mlab-modules/SDRX01/doc/src/img/signal2.jpg

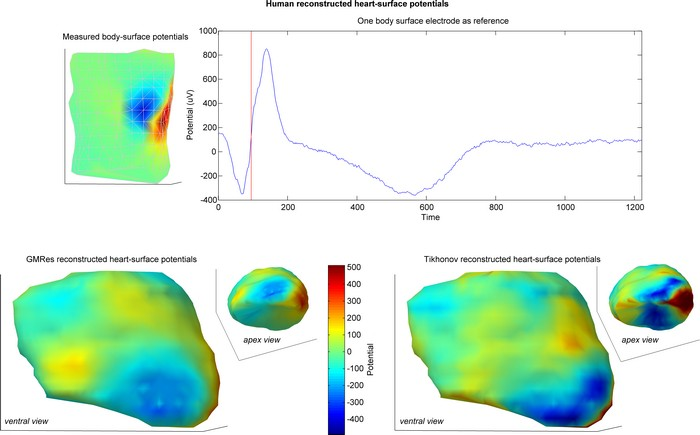
doc/src/img/signal2.jpg
