mlab-modules/SDRX01/hw/cam_doc/SDRX.pdf

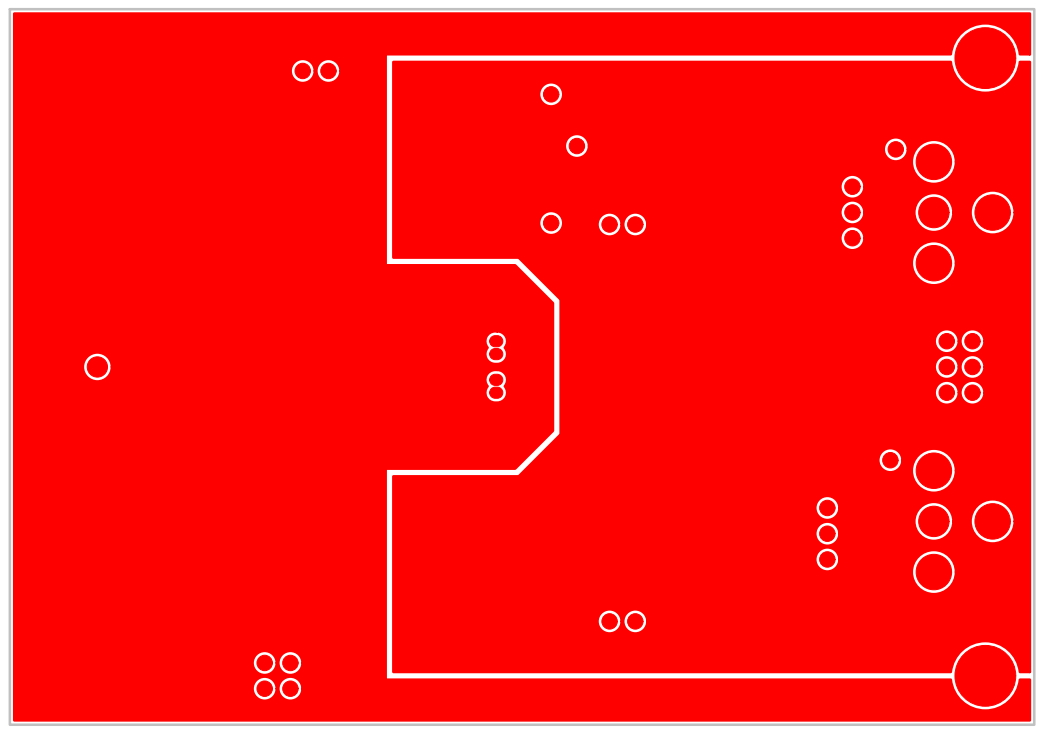
[picture p22: page 1]
M1M¹x1; M2M²x1; M4M⁴x1; M5M⁵x1; P1P¹x1 P¹x2; P¹x3

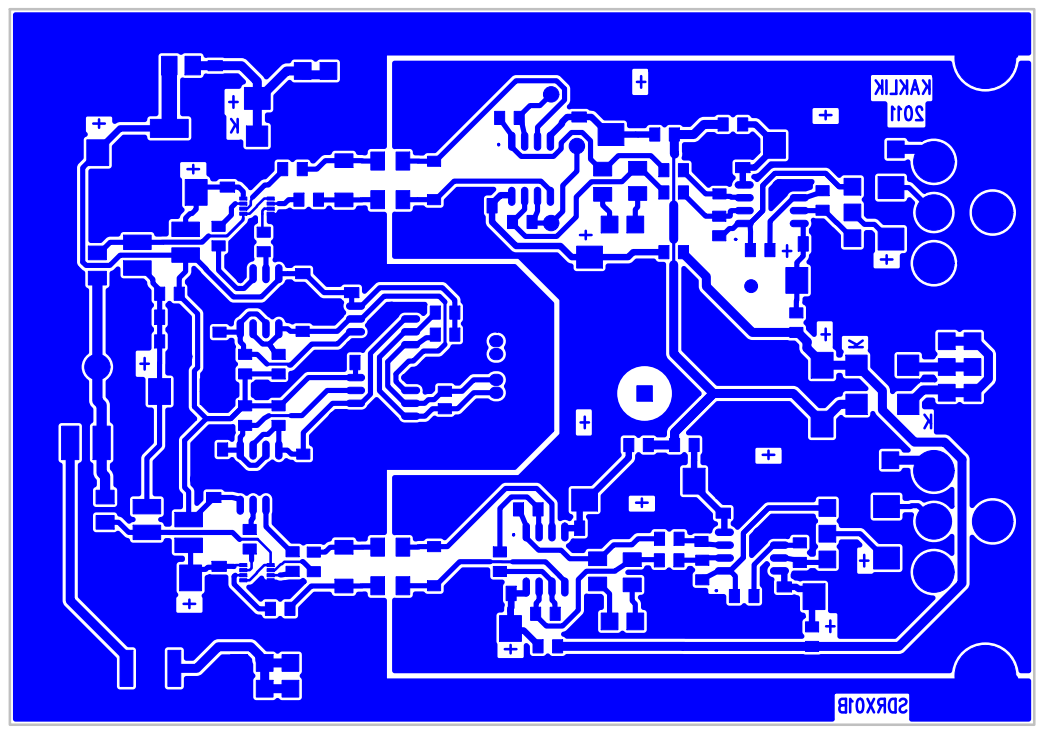
[picture p23: page 2]

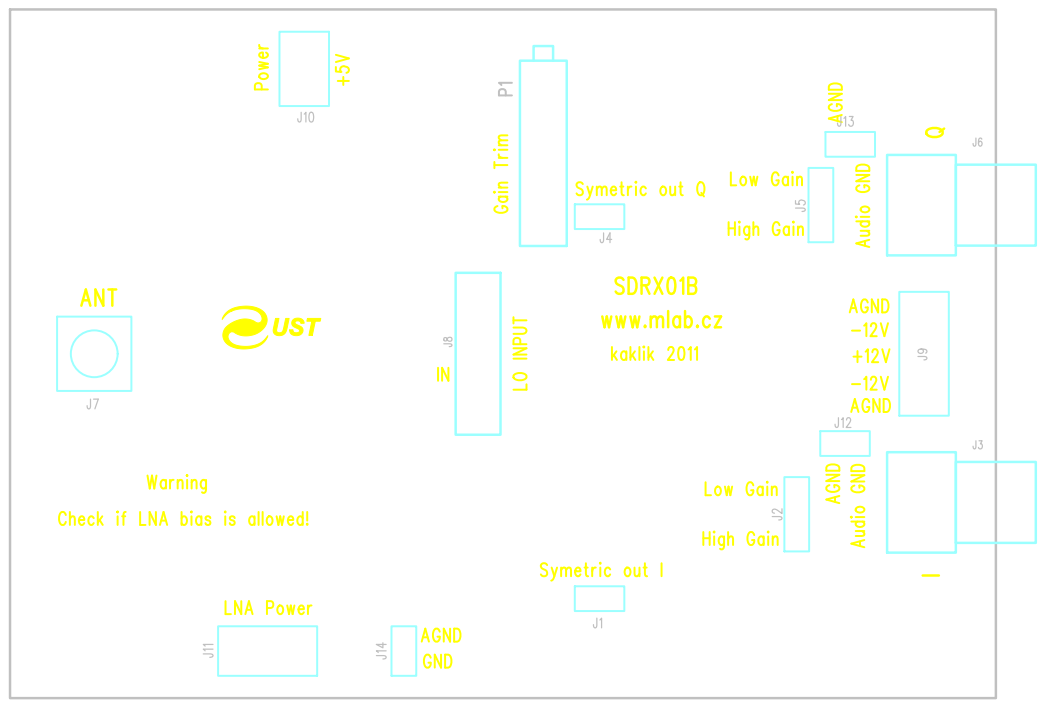
[picture p24: page 3]

Audio GND

Check if LNA bias is allowed!

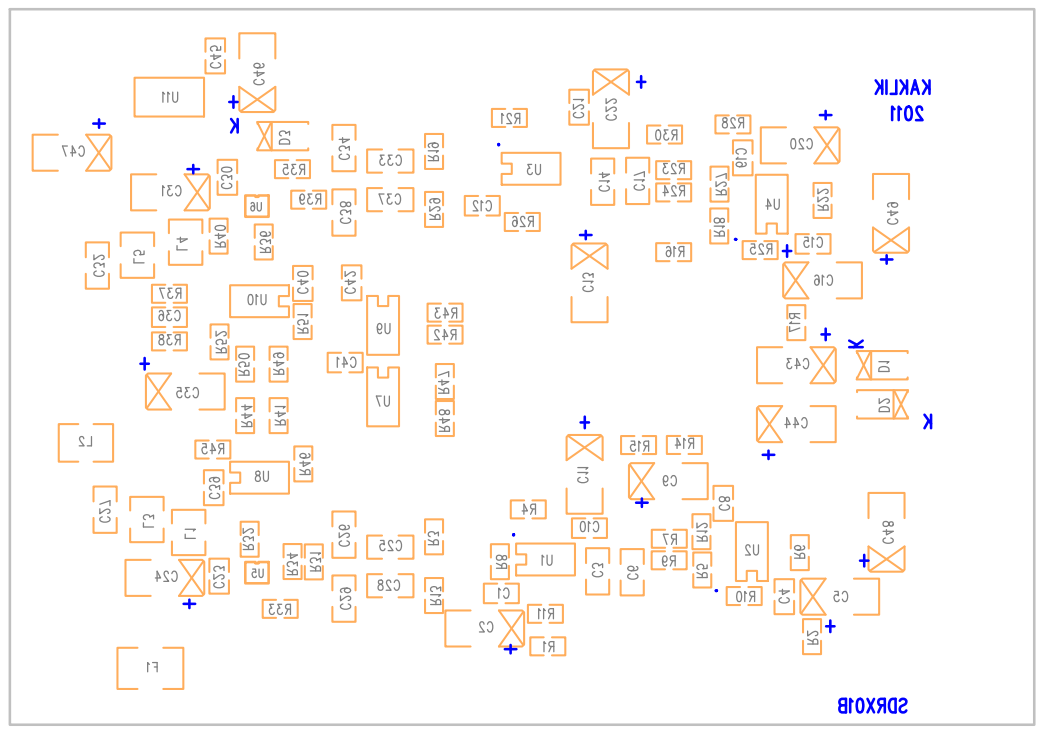
[picture p25: page 4]

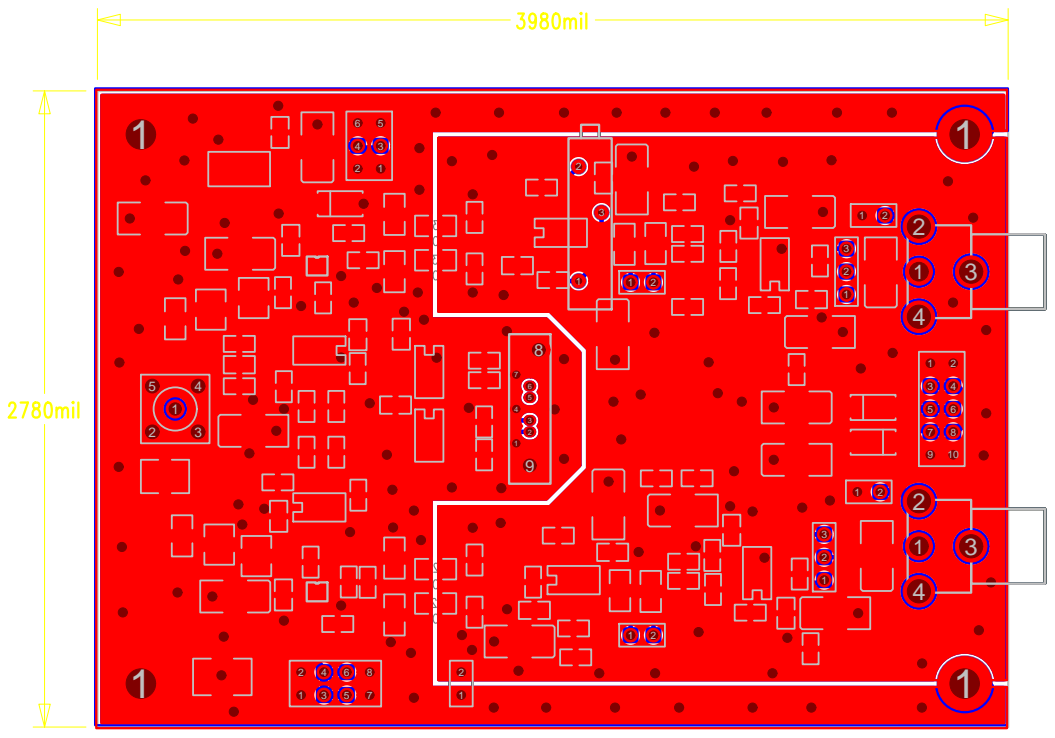
[picture p26: page 5]

Audio GND

Check if LNA bias is allowed!

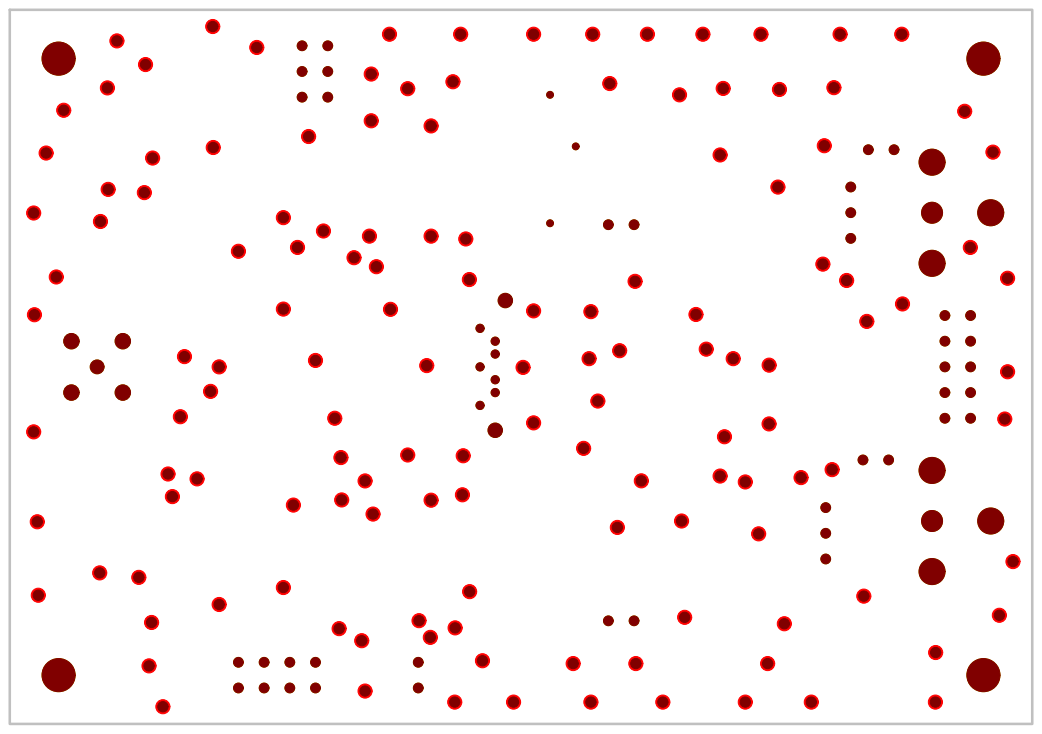
[picture p27: page 6]
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
