mlab-modules/SDRX01/doc/src/ADC_OZdual/OZdual.pdf

## POWER +VDD

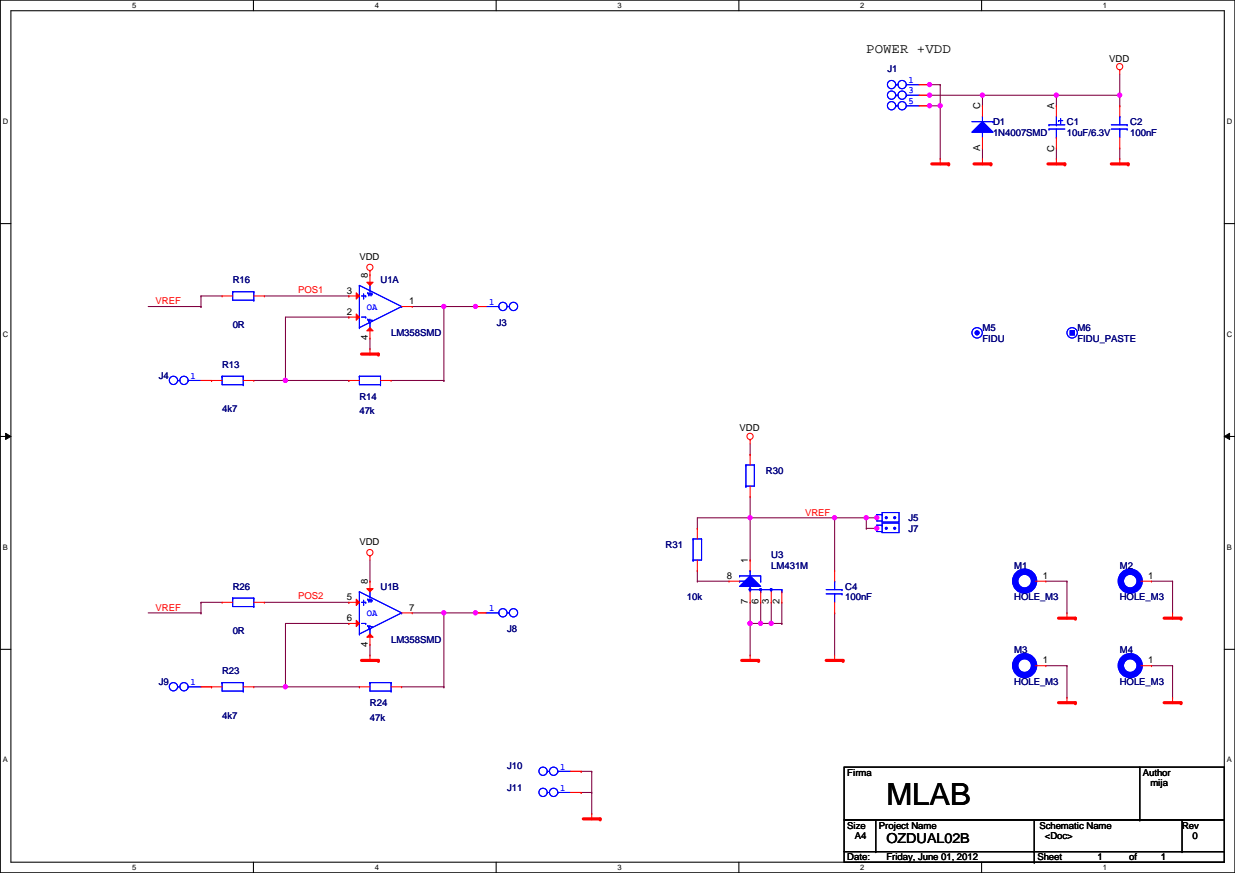
[picture p28: page 1]
