mlab-modules/SDRX01/hw/sch_pcb/AMP.pdf

# Generated by Foxit PDF Creator © Foxit Software

http://www.foxitsoftware.com For evaluation only.

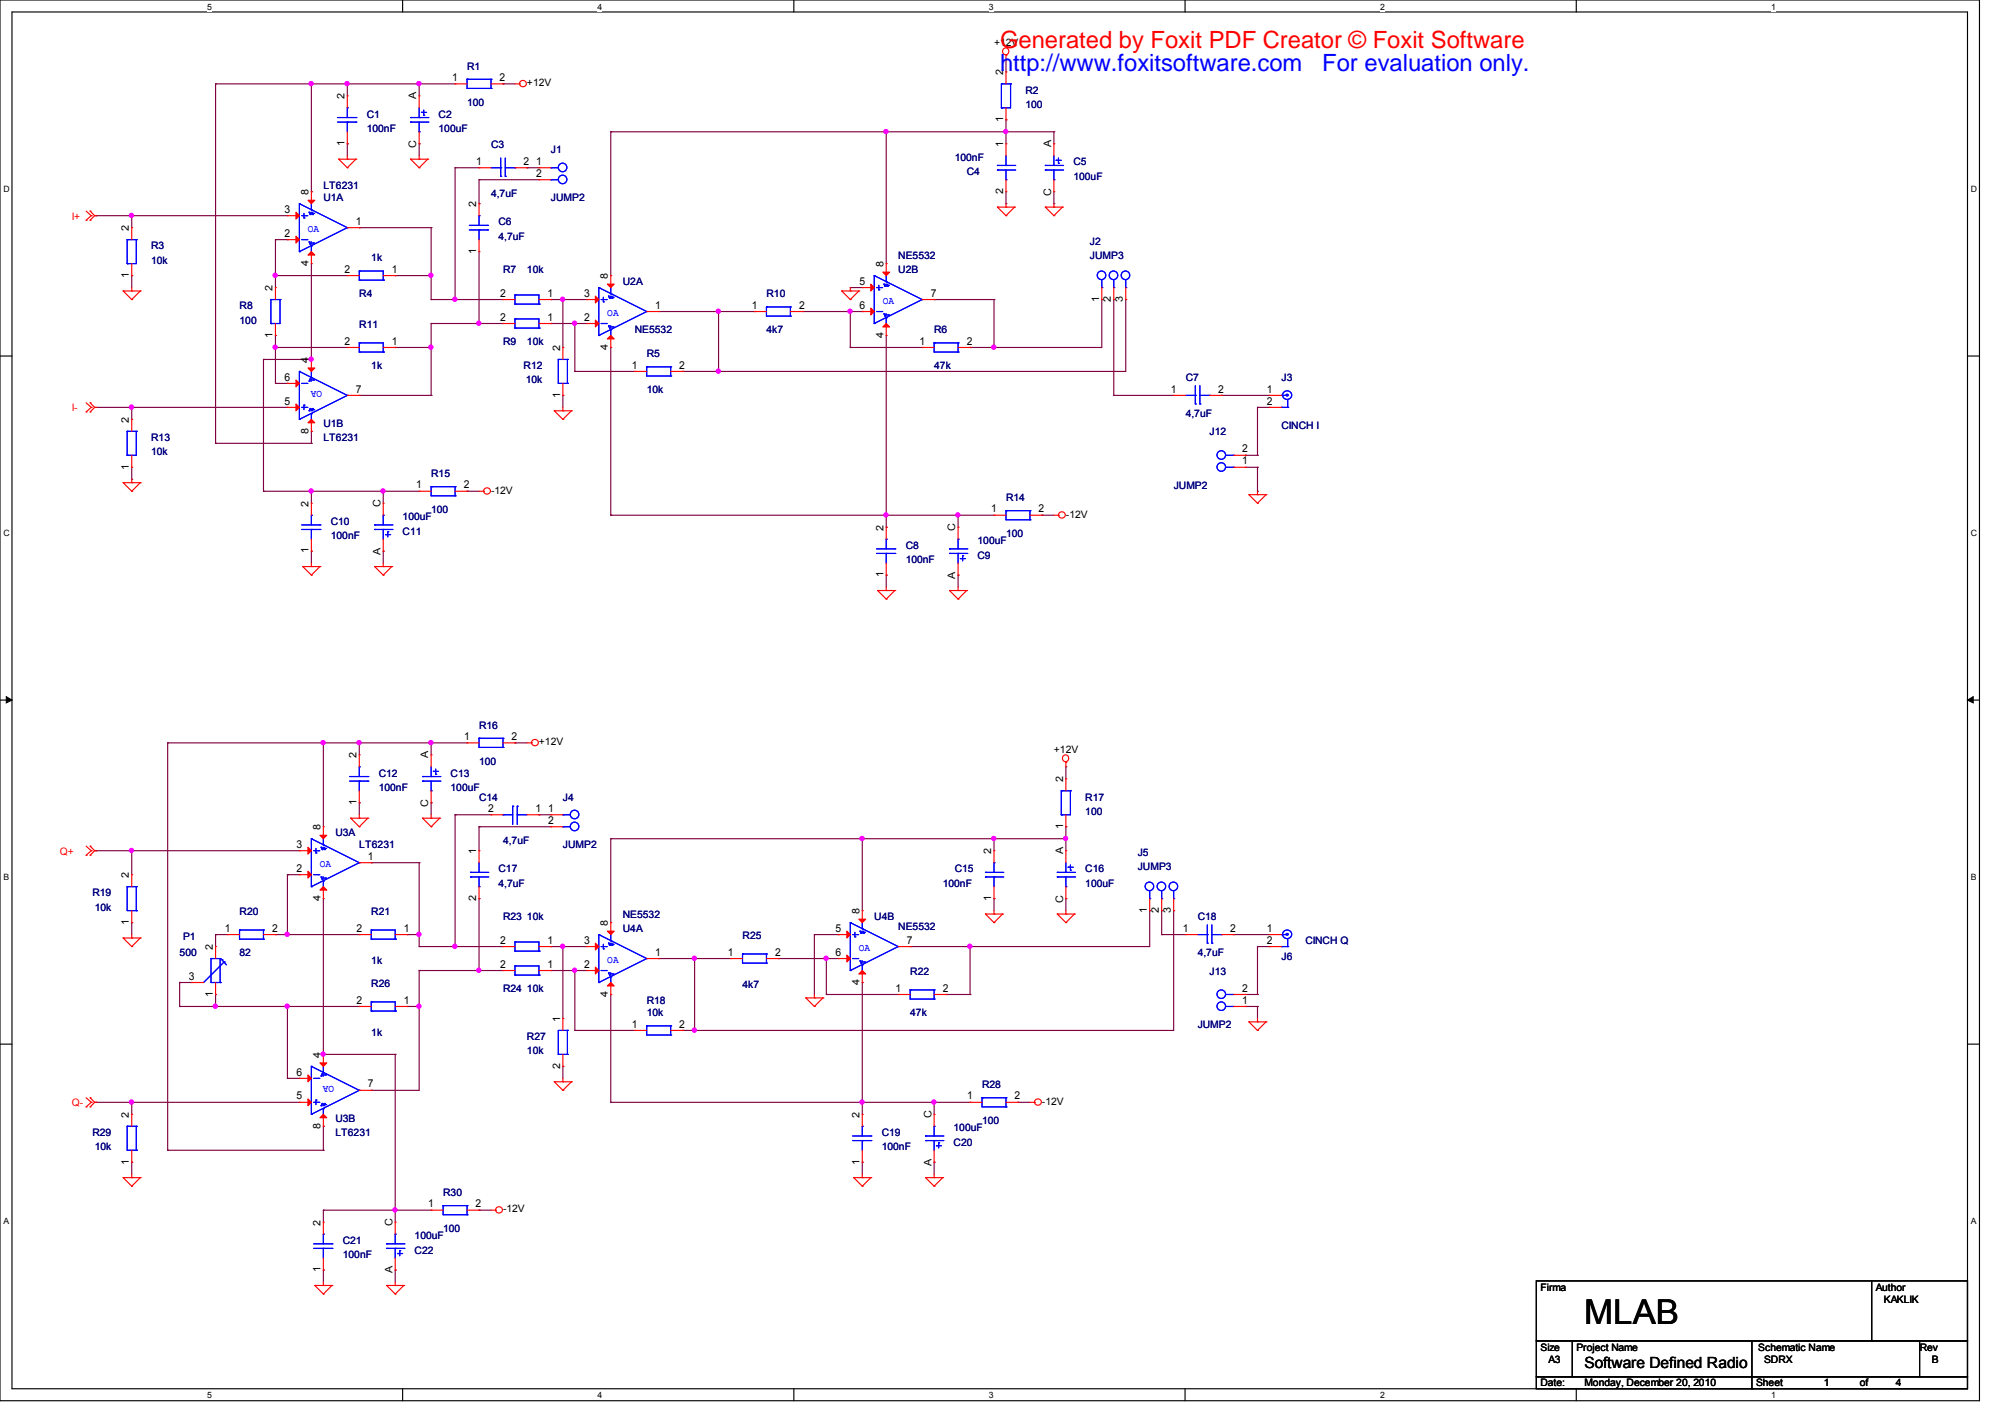
[picture p32: page 1]
