mlab-modules/SDRX01/hw/sch_pcb/MIXER.pdf

# Generated by Foxit PDF Creator © Foxit Software

http://www.foxitsoftware.com For evaluation only.

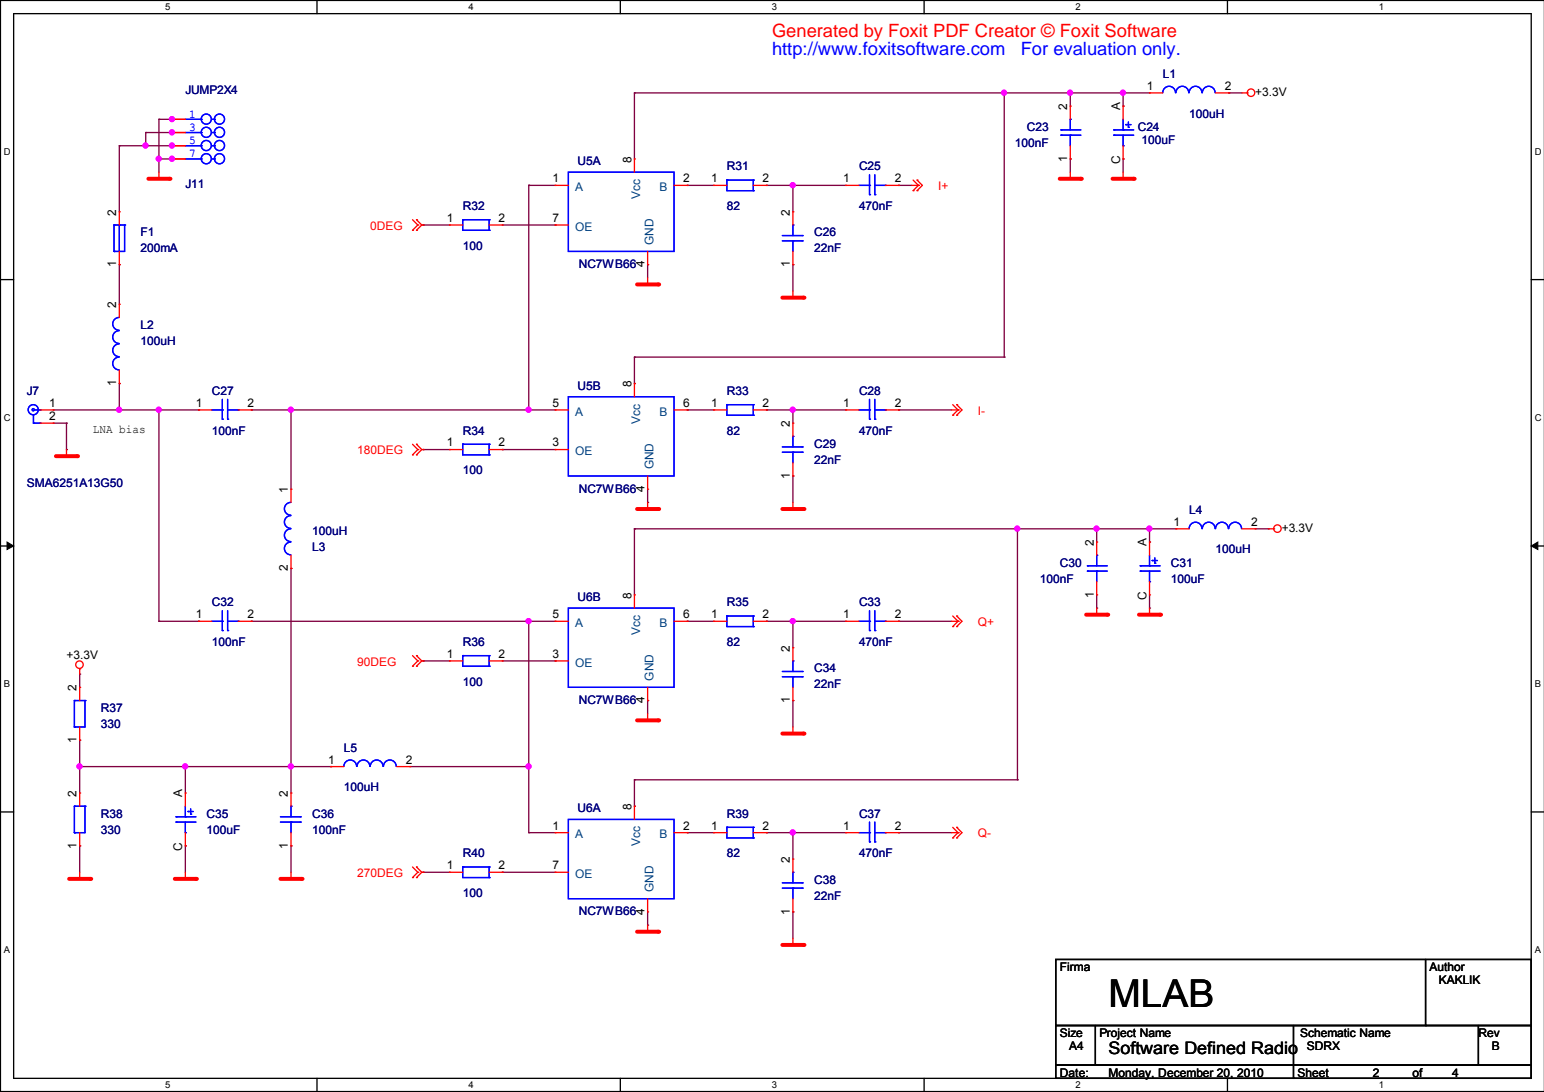
[picture p33: page 1]
