mlab-modules/SDRX01/hw/sch_pcb/PHASER.pdf

# Generated by Foxit PDF Creator © Foxit Software

http://www.foxitsoftware.com For evaluation only.

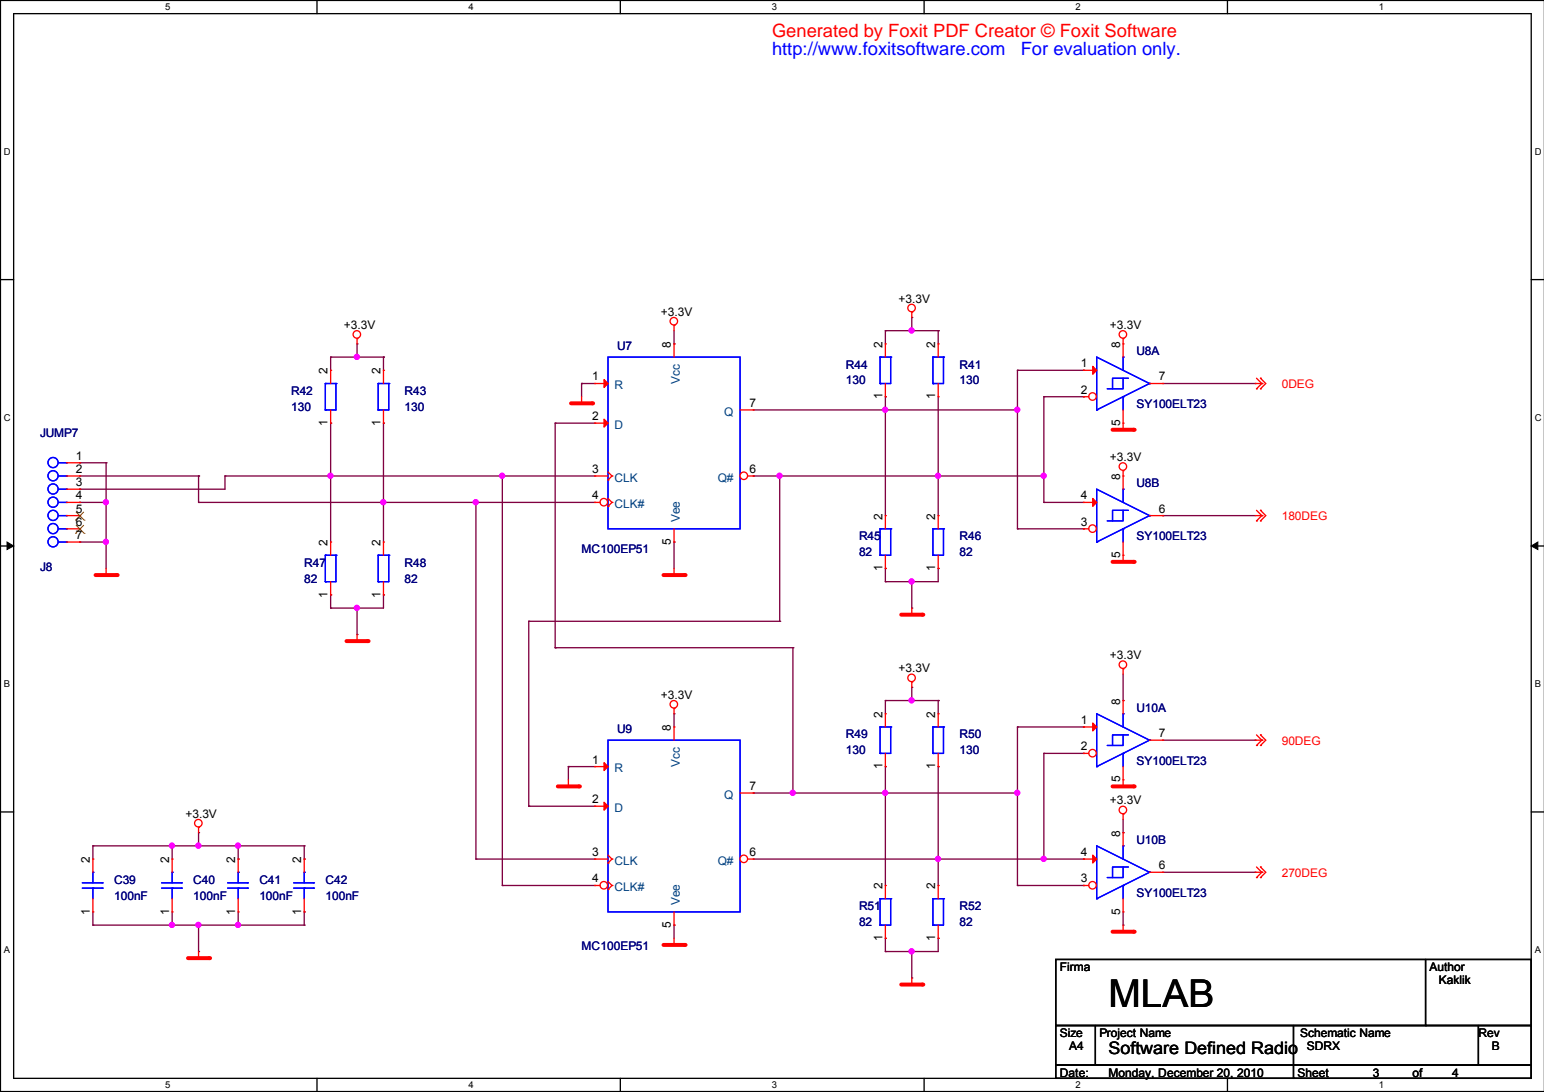
[picture p34: page 1]
