mlab-modules/SDRX01/hw/sch_pcb/POWER.pdf

# Generated by Foxit PDF Creator © Foxit Software

http://www.foxitsoftware.com For evaluation only.

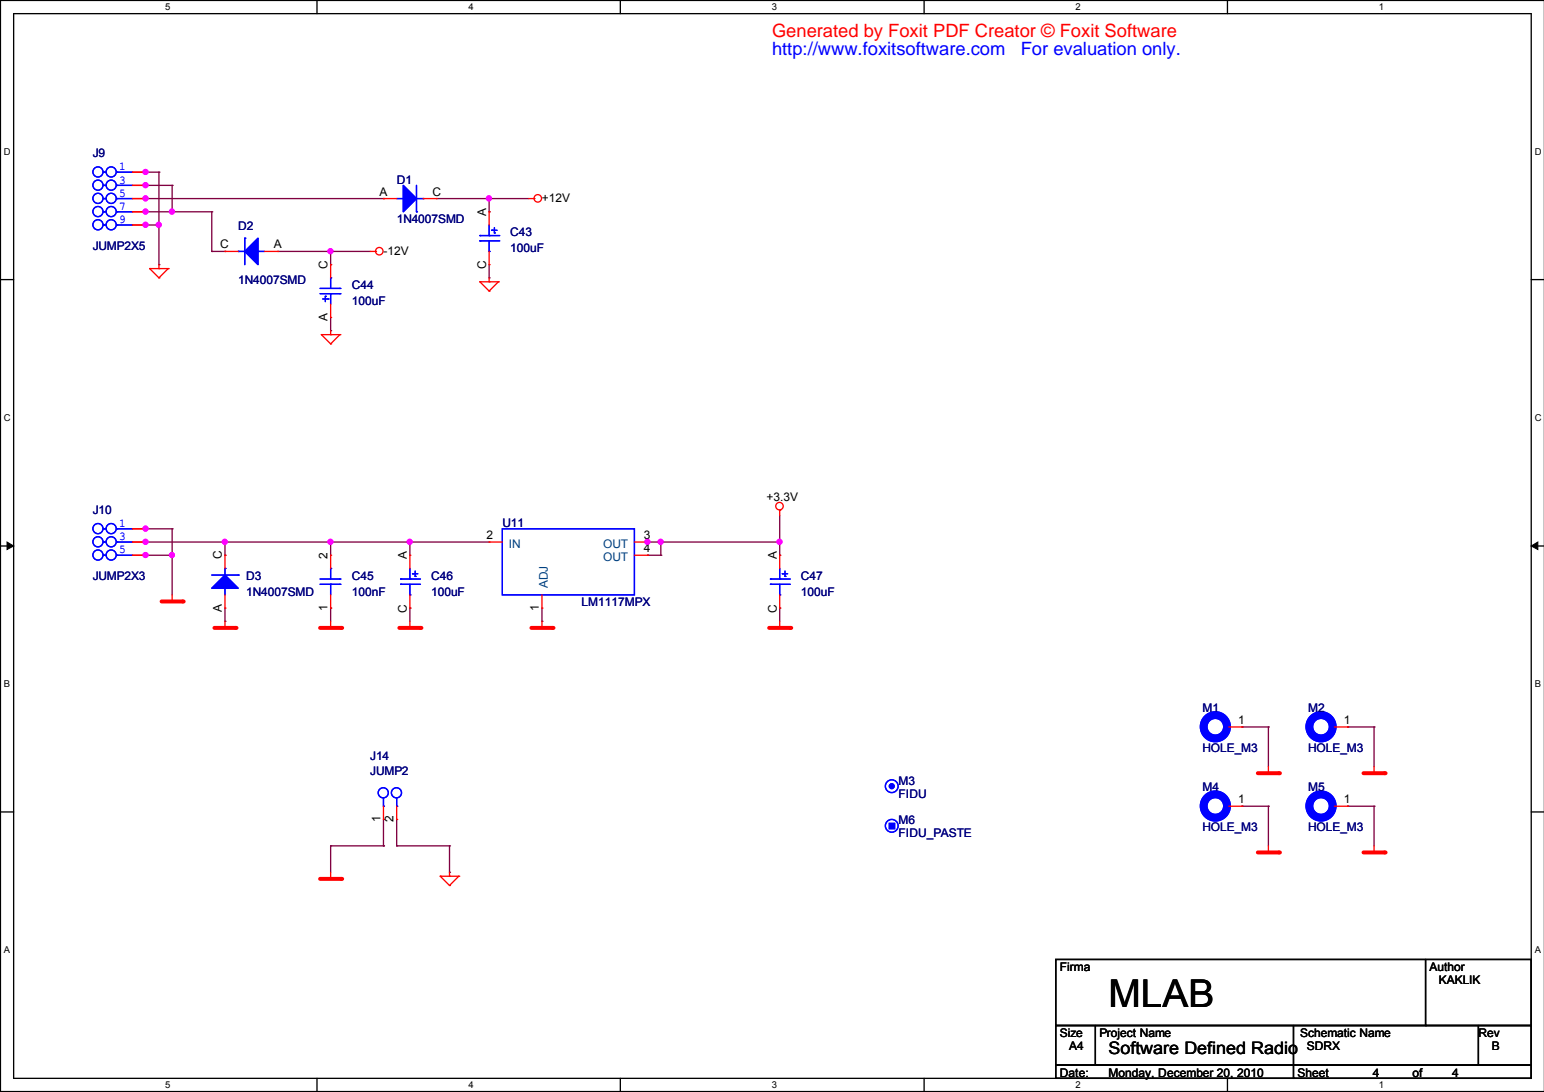
[picture p35: page 1]
