mlab-modules/SDRX01/hw/sch_pcb/sdrx.pdf

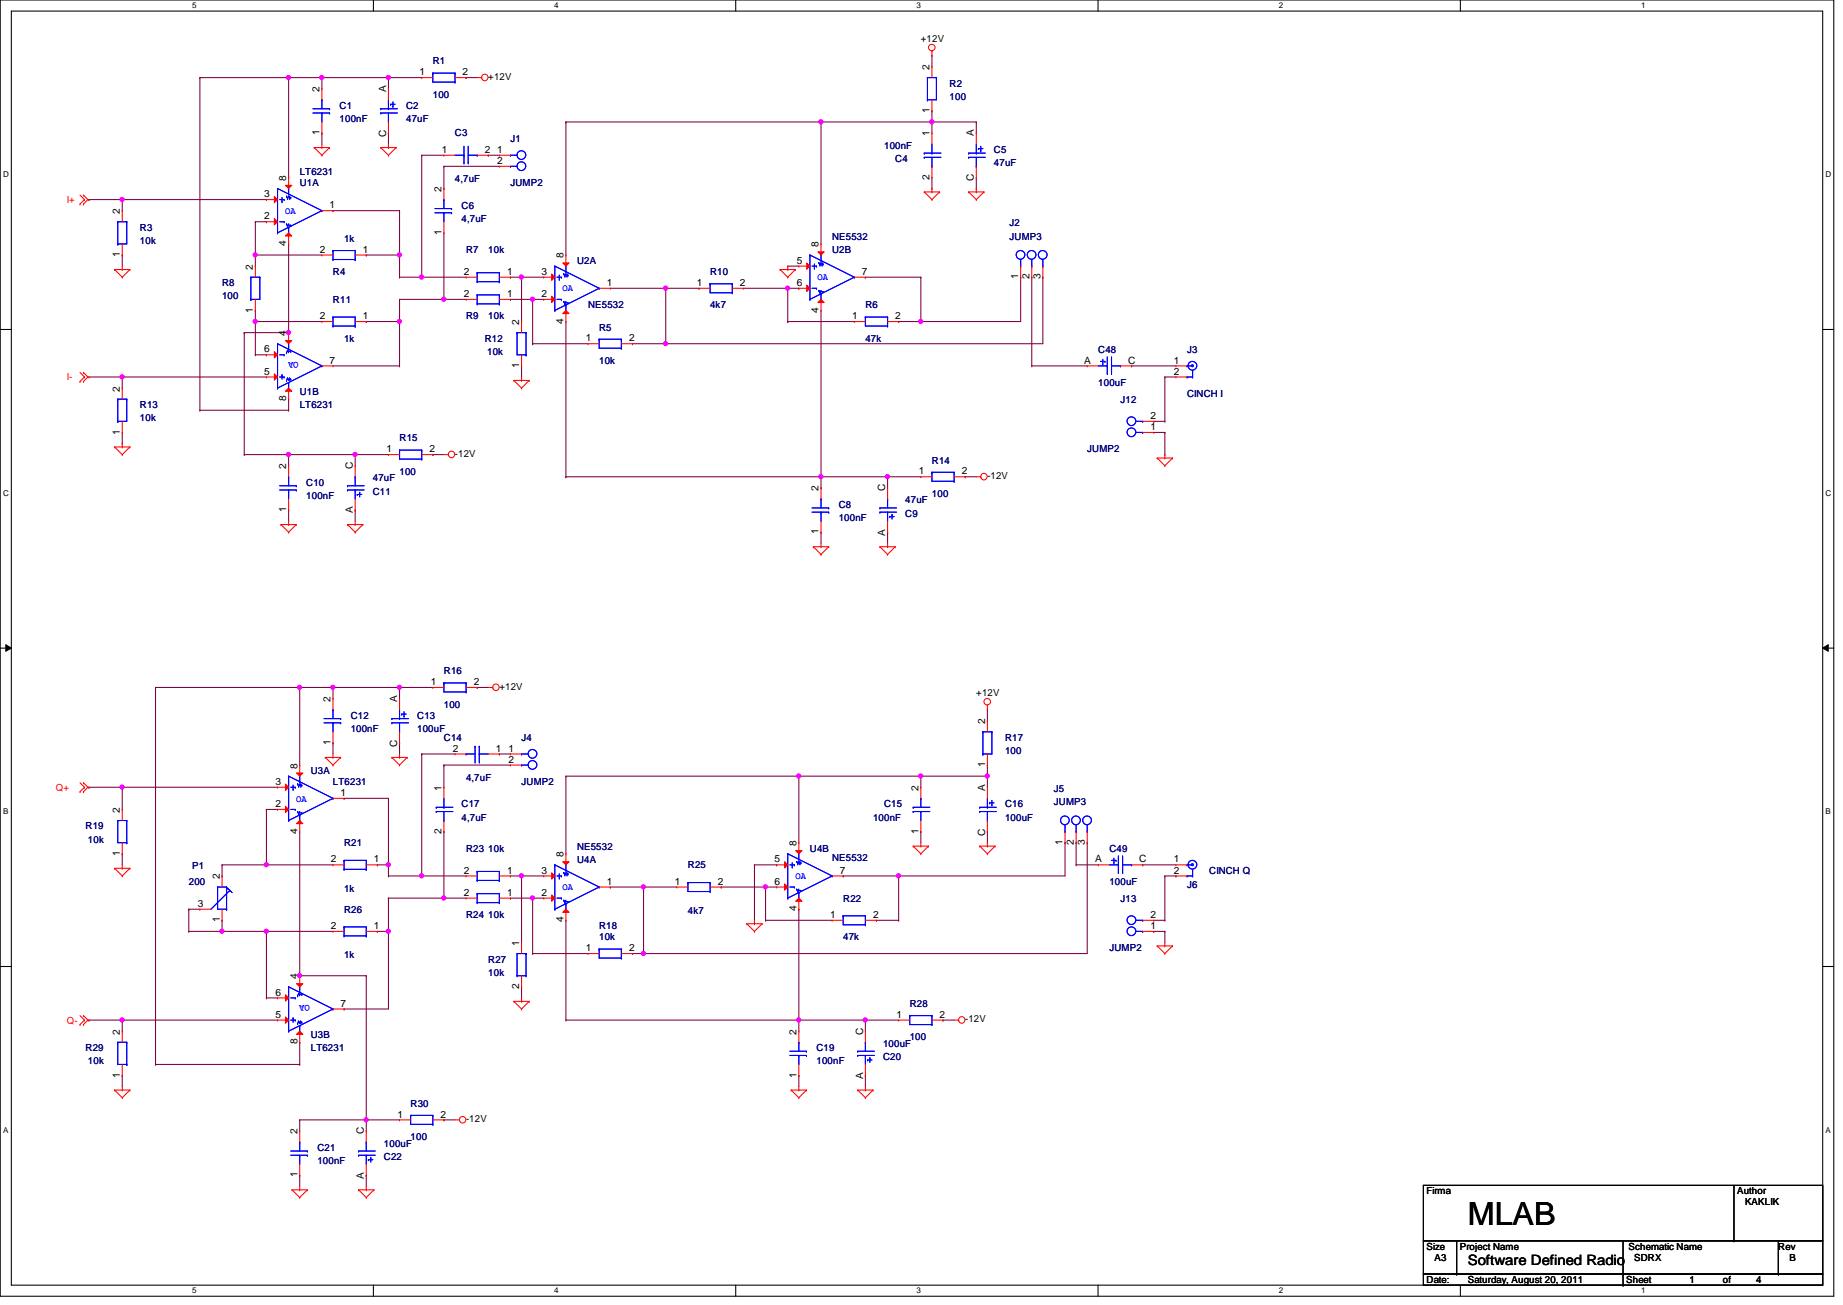
[picture p36: page 1]

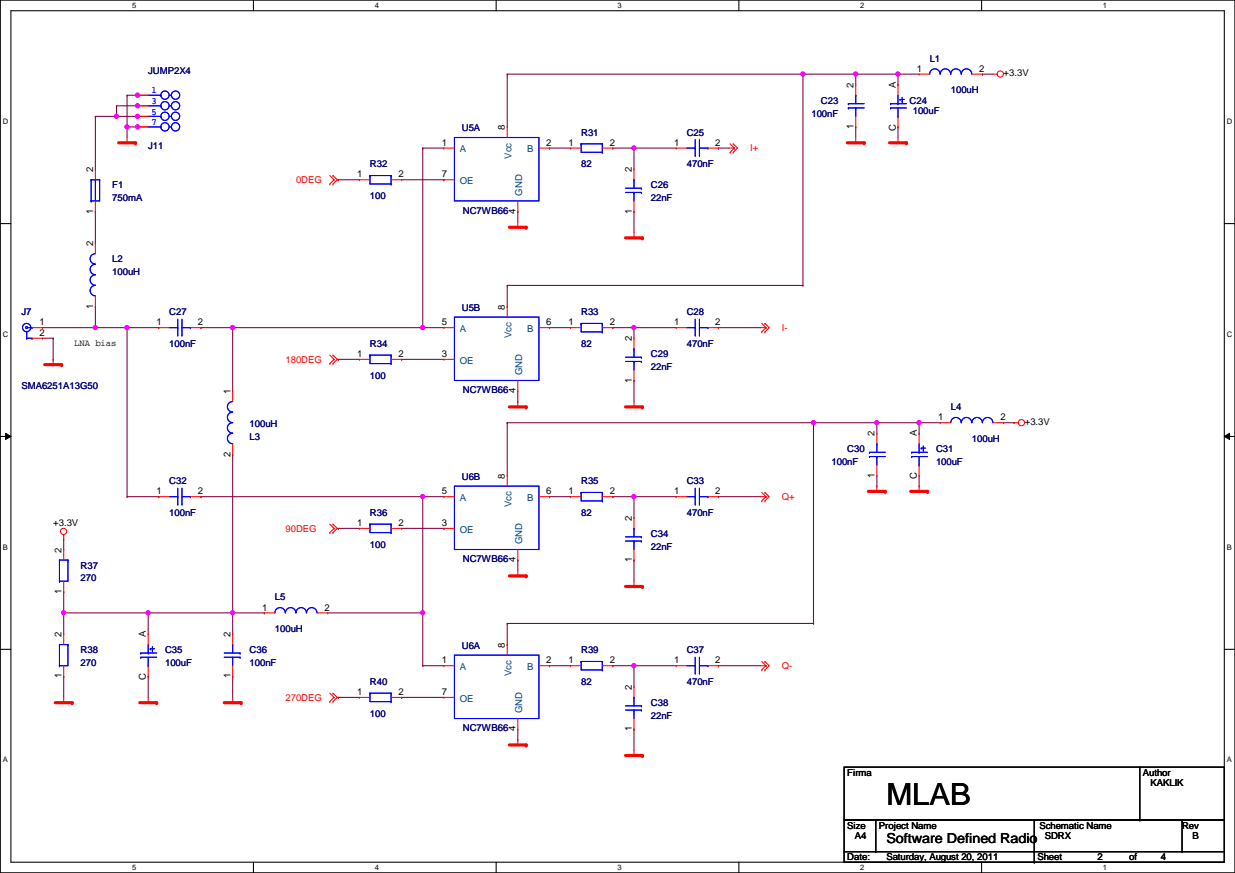
[picture p37: page 2]

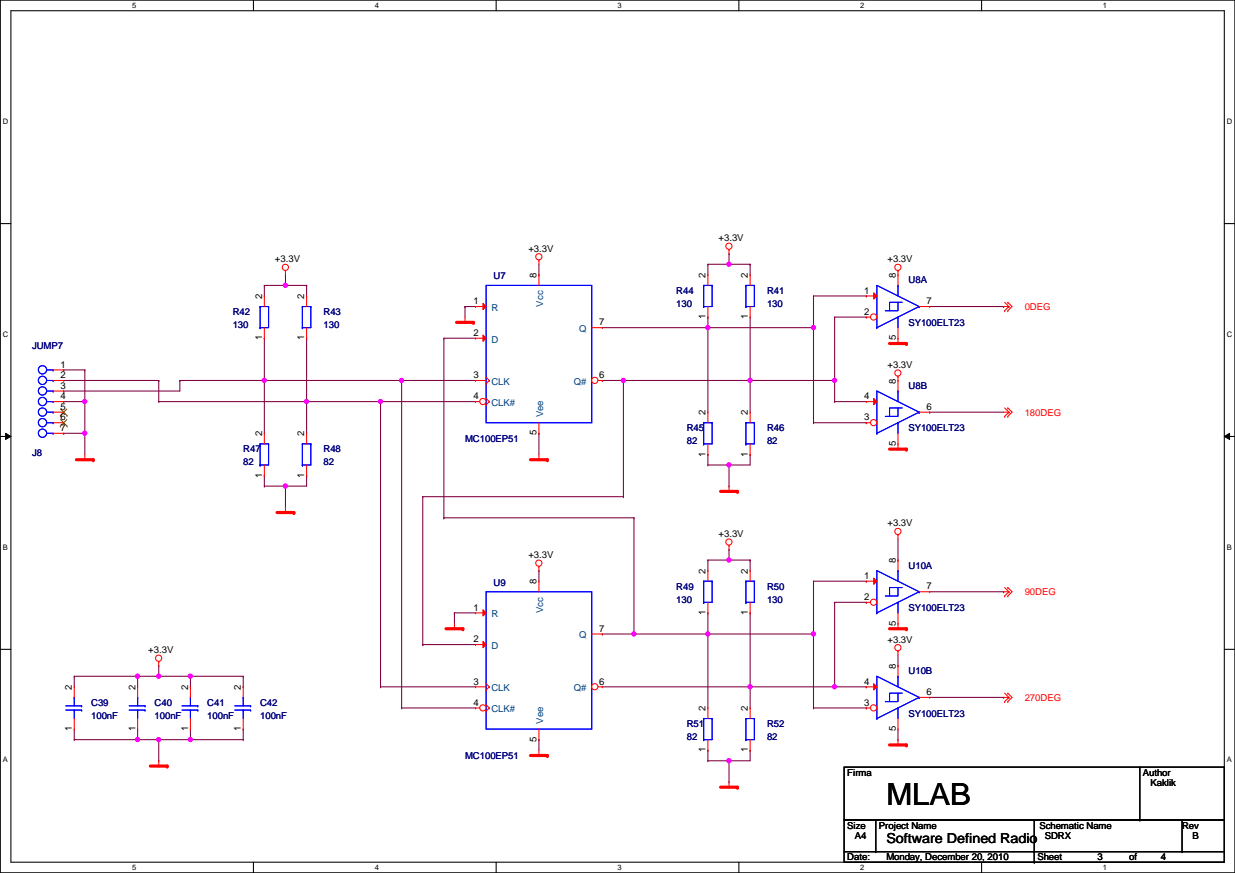
[picture p38: page 3]

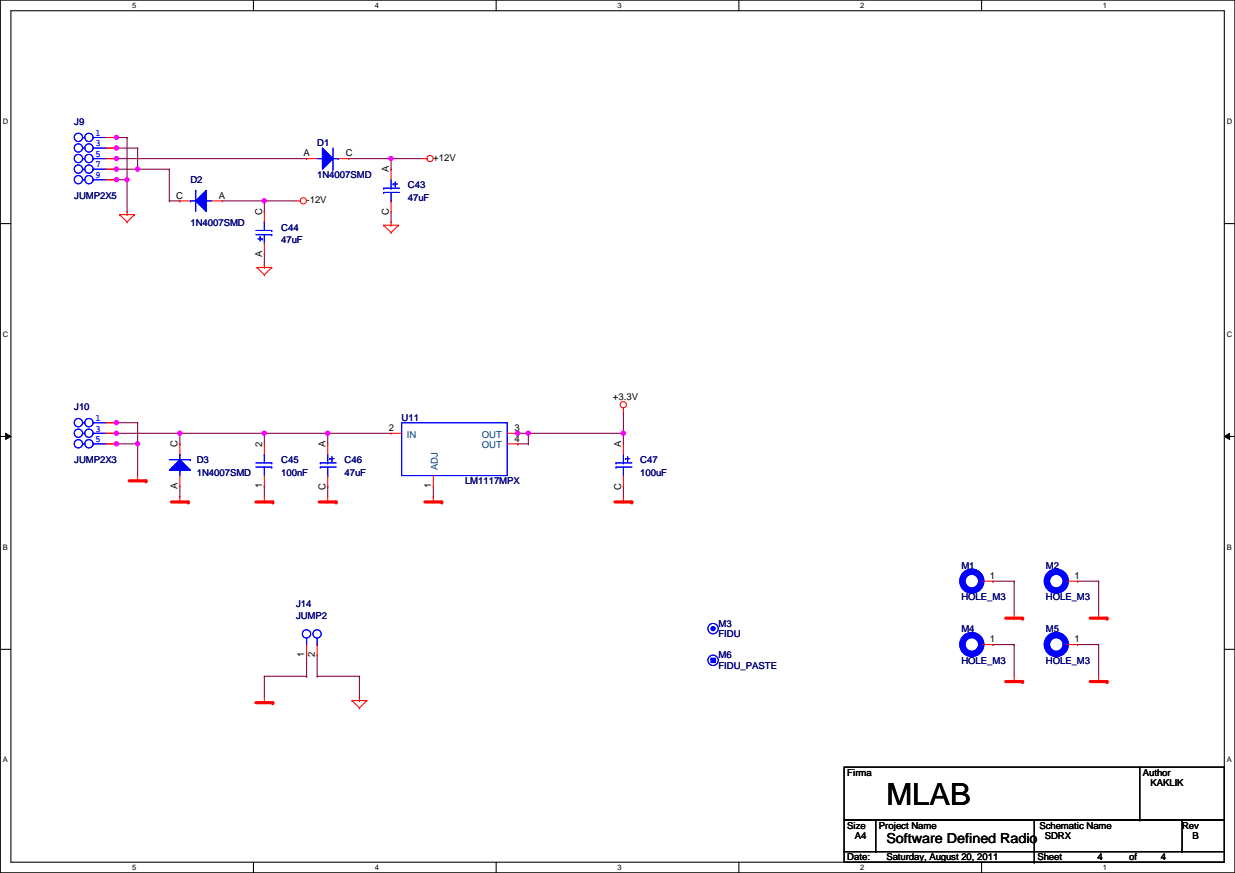
[picture p39: page 4]
