mlab-modules/SDRX01/CAM_DOC/V1.pdf

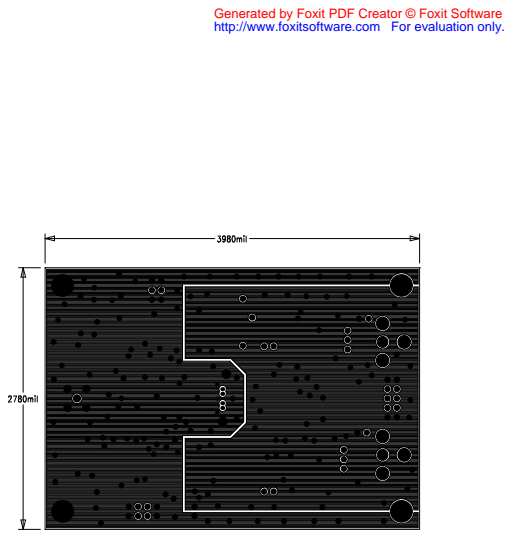
[picture p40: page 1]

Generated by Foxit PDF Creator © Foxit Software
http://www.foxitsoftware.com For evaluation only.
